weinkyls/epsilonbot/additional_files/datasheets/usb pd/PowerDeliveryBoardUSB-C_Dimension.png

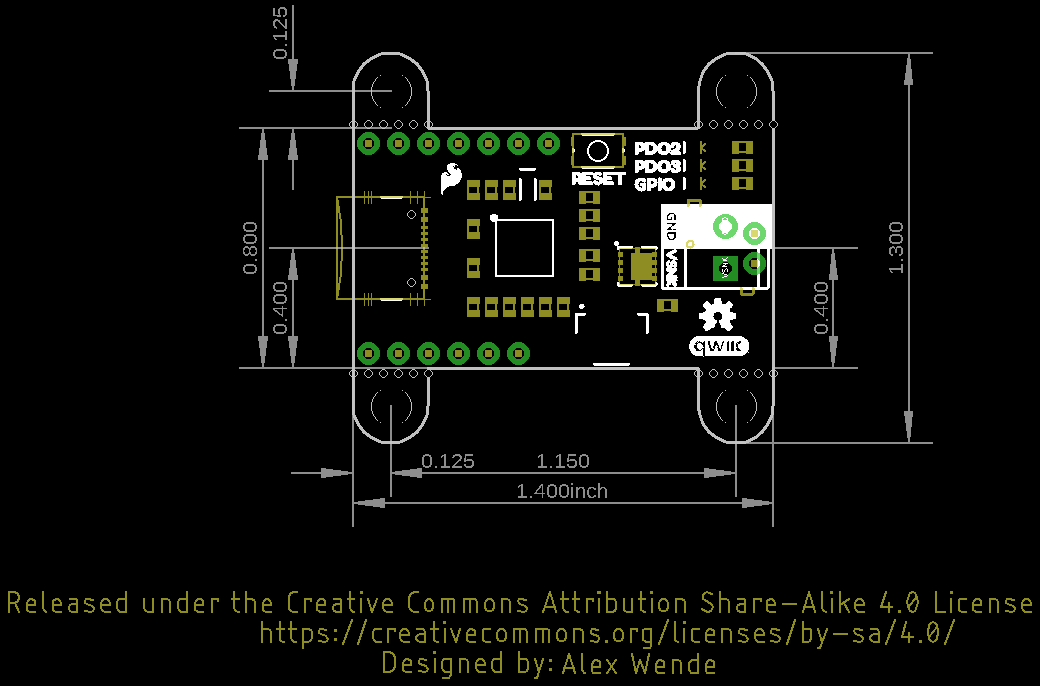
additional_files/datasheets/usb pd/PowerDeliveryBoardUSB-C_Dimension.png
