weinkyls/epsilonbot/images/PowerFlowchart.drawio.png

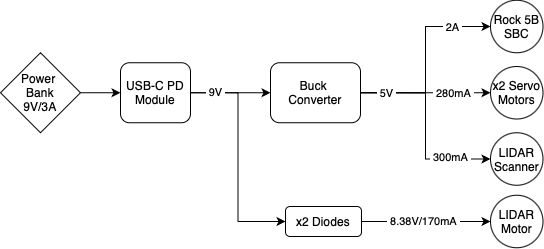
images/PowerFlowchart.drawio.png
